aerohstudios/aeroh-link/cad/case/front_enclosure/enclosure_front_plate_screw_mount_4.3mf

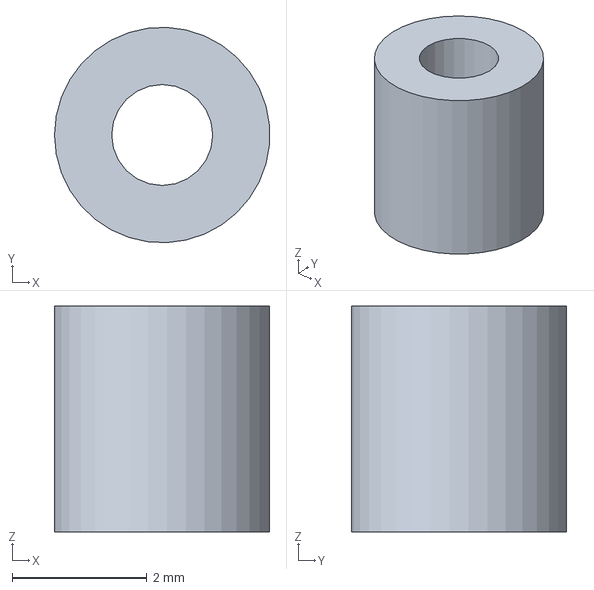
[picture p27: CAD file, 2023-02-09]
cad/case/front_enclosure/enclosure_front_plate_screw_mount_4.3mf
3.19 x 3.20 x 3.35 mm
